blannoy/Woordklok/doc/pictures/parts.jpg

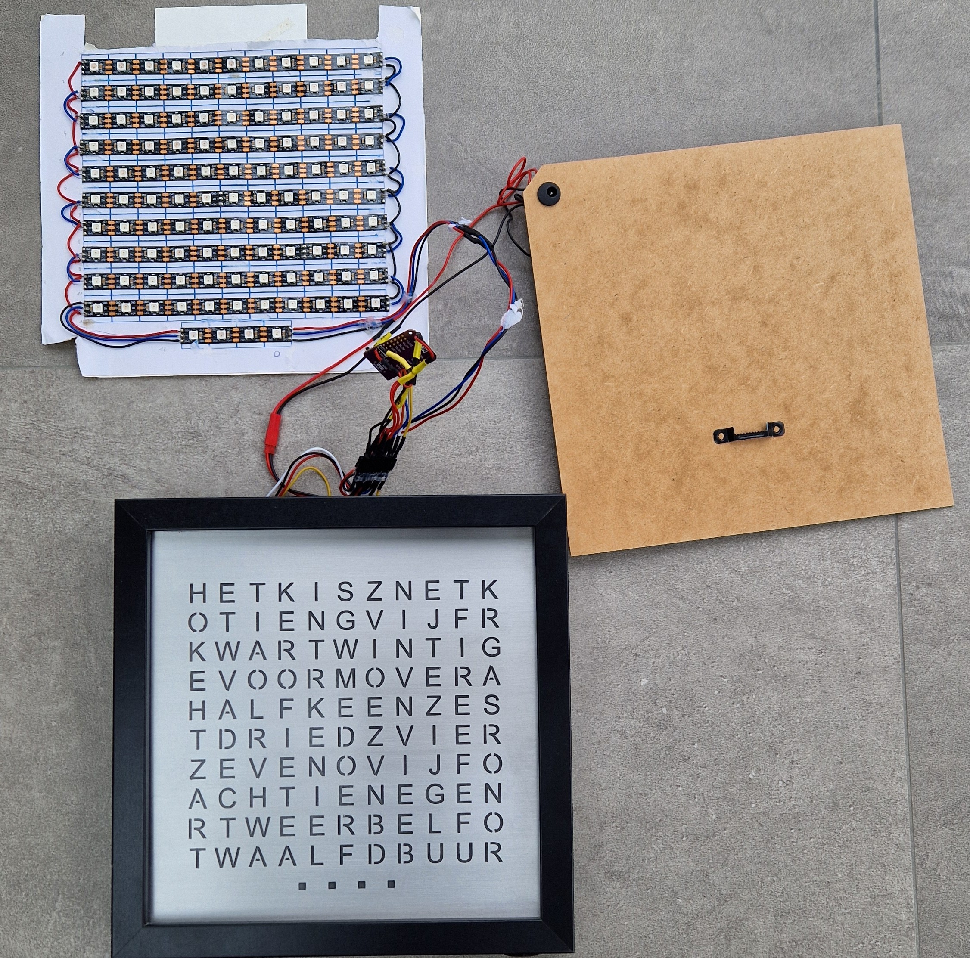
doc/pictures/parts.jpg
